lachlanchen/OpenHI/comparisons/align_background_vs_reference_code/DATASETS_DUAL.md

# Dual Three‑Panel Overlays (Blank + Sample + GT)

This note records the dual‑overlay figure that combines:
- **Blank** (light‑source only)
- **Sample** (dicot stem; previously mislabeled “sanqin”)
- **Ground‑truth spectrometer SPD**

The figure is generated by a dedicated script:
- `comparisons/align_background_vs_reference_code/compare_publication_three_panel_dual.py`

## Dataset Pairing (Lumileds)

**Blank segment**
- `scan_angle_20_lumileds/angle_20_blank_20250922_170433/angle_20_blank_event_20250922_170433_segments/Scan_1_Forward_events.npz`

**Sample segment (dicot stem)**
- `scan_angle_20_lumileds/angle_20_sanqin_20250922_170630/angle_20_sanqin_event_20250922_170630_segments/Scan_1_Forward_events.npz`

**Ground‑truth SPD**
- `comparisons/reference_spectrum_lumileds/USB2F042671_16-04-56-391.txt`

## Command Used (current best)

This run uses **auto‑shift by correlation** between the GT derivative and the
sample derivative. The auto‑shift consistently finds a shift near **‑49 nm**,
matching the manual observation but without hardcoding the value.

```bash
python comparisons/align_background_vs_reference_code/compare_publication_three_panel_dual.py \
  --segment-blank scan_angle_20_lumileds/angle_20_blank_20250922_170433/angle_20_blank_event_20250922_170433_segments/Scan_1_Forward_events.npz \
  --segment-sample scan_angle_20_lumileds/angle_20_sanqin_20250922_170630/angle_20_sanqin_event_20250922_170630_segments/Scan_1_Forward_events.npz \
  --gt_files comparisons/reference_spectrum_lumileds/USB2F042671_16-04-56-391.txt \
  --step_ms 2.0 --bin_ms 5.0 \
  --sensor_width 1280 --sensor_height 720 \
  --label-blank "Blank" --label-sample "Dicot stem" \
  --auto-shift-sample-corr --shift-range 120 --shift-step 1 \
  --suffix lumileds_blank_dicot_autoshift \
  --output_root comparisons/align_background_vs_reference_code
```

**Output**
- `comparisons/align_background_vs_reference_code/publication_20260206_213134/three_panel_dual_5ms_Scan_1_Forward_Scan_1_Forward_lumileds_blank_dicot_autoshift.png`
- `comparisons/align_background_vs_reference_code/publication_20260206_213134/three_panel_dual_5ms_Scan_1_Forward_Scan_1_Forward_lumileds_blank_dicot_autoshift_mapping.json`

## Alignment Logic (what changed and why)

Originally, the sample was aligned using **plateau‑based affine scaling**, which could push the curve below 0 and
produce unstable results. This is not robust when sample intensity has real absorption and does not share the
same plateau values as the blank/GT.

The alignment logic is now a **pure wavelength shift** for the sample:

- `--auto-shift-sample-corr` (recommended): shifts the sample to maximize correlation between
  the GT derivative and the sample derivative.
- `--sample-shift-nm` (manual): fixed shift in nm if you want full control.
- `--auto-shift-sample-left-edge` (optional): align left edge only.

This is **more stable** and keeps the sample curve shape intact while aligning the left edge
and overall derivative structure. No amplitude scaling is applied anymore.

## Notes

- The script uses **blank** to define the wavelength–time mapping (λ(t)).
- The sample shares the same mapping but can be shifted with `--sample-shift-nm`.
- If you want to try automatic left‑edge alignment, replace `--sample-shift-nm -50` with
  `--auto-shift-sample-left-edge`.
