lachlanchen/OpenHI/comparisons/align_background_vs_reference_code/publication_20260206_220756/background_trace_multibin_Scan_1_Forward_events.png

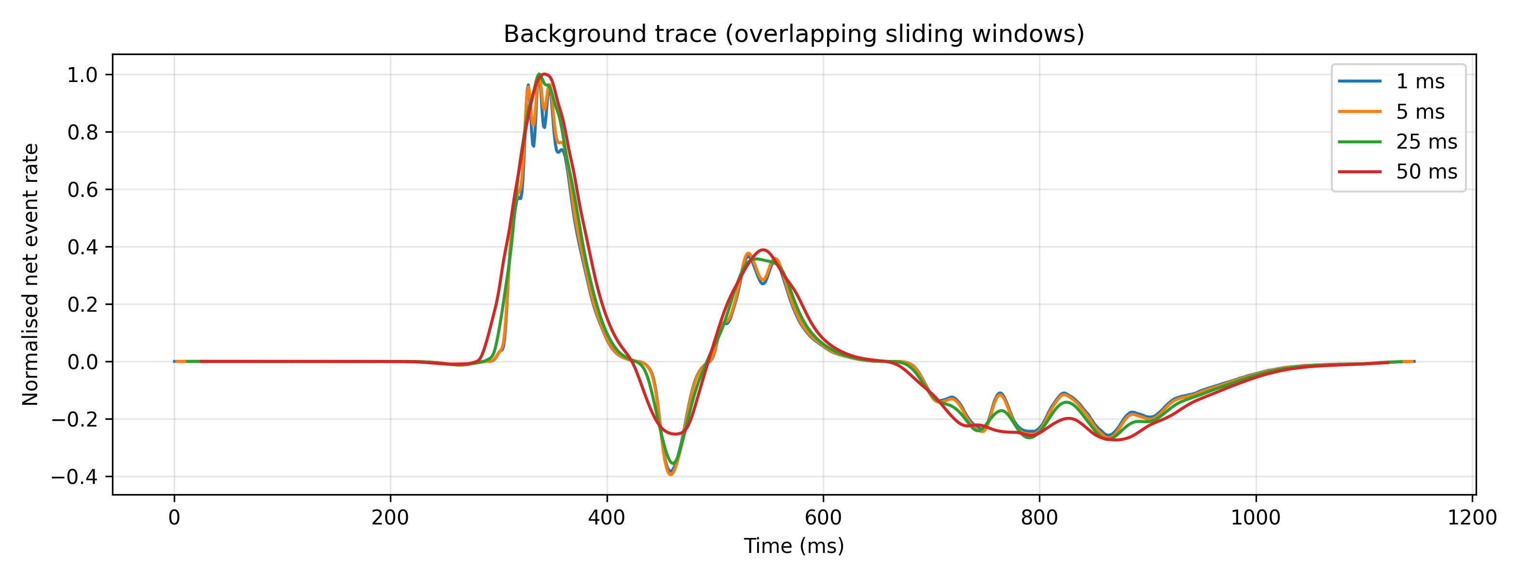
comparisons/align_background_vs_reference_code/publication_20260206_220756/background_trace_multibin_Scan_1_Forward_events.png
