lachlanchen/OpenHI/3D/Optional4F3D/Lens C holder.stl

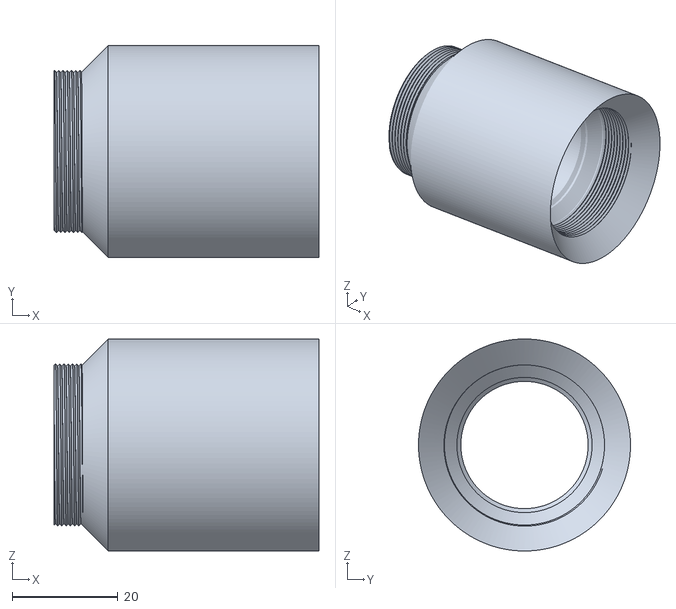
[picture p22: CAD file, 2026-03-04]
3D/Optional4F3D/Lens C holder.stl
50.0 x 40.0 x 40.0
