lachlanchen/OpenHI/3D/OpenHICoreModule3D/Motor cap.stl

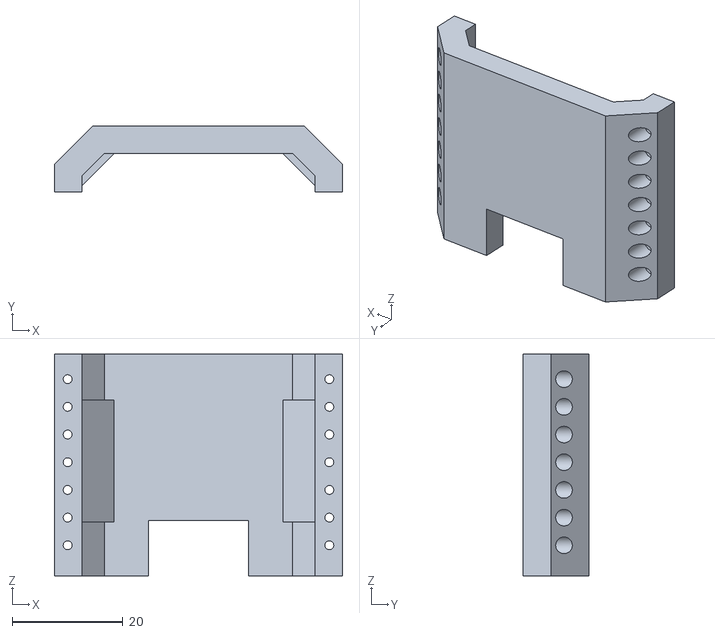
[picture p23: CAD file, 2026-03-04]
3D/OpenHICoreModule3D/Motor cap.stl
52.0 x 12.0 x 40.0
