lachlanchen/OpenHI/3D/OpenHICoreModule3D/Collimator holder FHPLP.stl

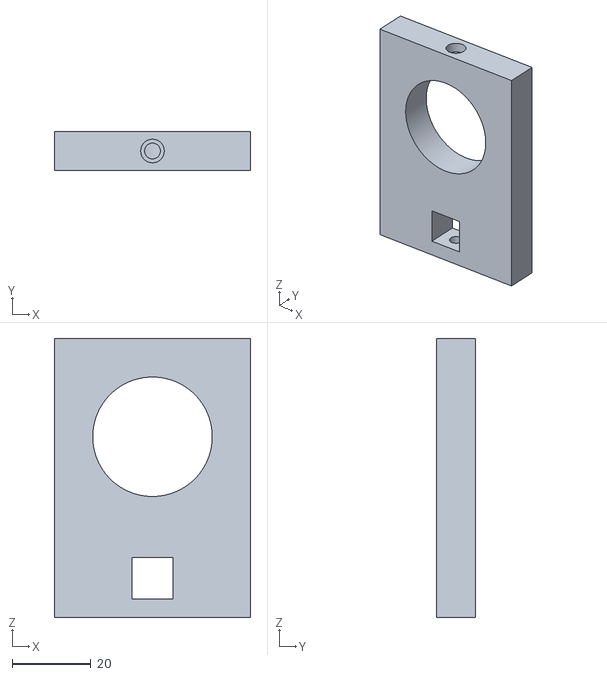
[picture p24: CAD file, 2026-03-04]
3D/OpenHICoreModule3D/Collimator holder FHPLP.stl
50.0 x 10.0 x 71.0
