lachlanchen/OpenHI/3D/OpenHICoreModule3D/Collimator cap.stl

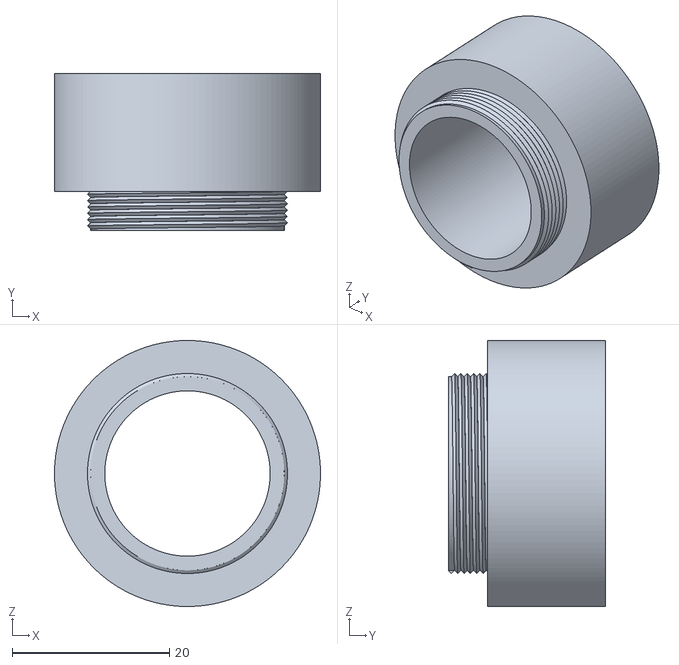
[picture p25: CAD file, 2026-03-04]
3D/OpenHICoreModule3D/Collimator cap.stl
33.8 x 20.0 x 33.8
