lachlanchen/OpenHI/3D/OpenHICoreModule3D/Motor holder.stl

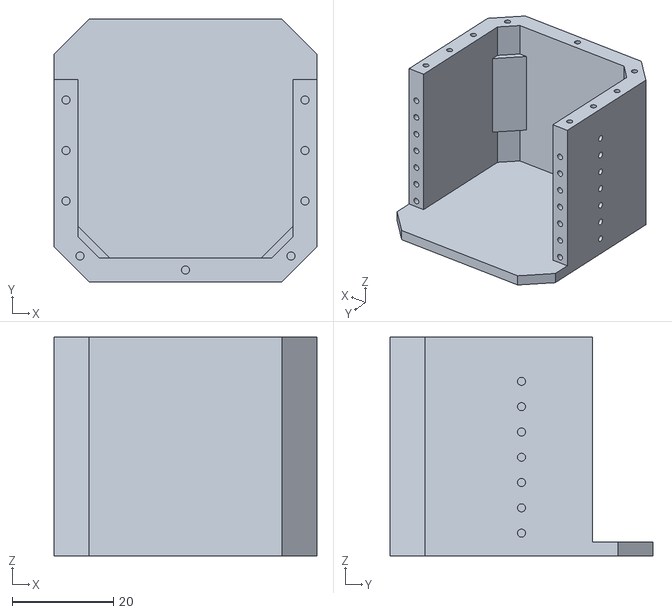
[picture p26: CAD file, 2026-03-04]
3D/OpenHICoreModule3D/Motor holder.stl
52.0 x 52.0 x 43.2
