lachlanchen/OpenHI/3D/OpenHICoreModule3D/LED holder.stl

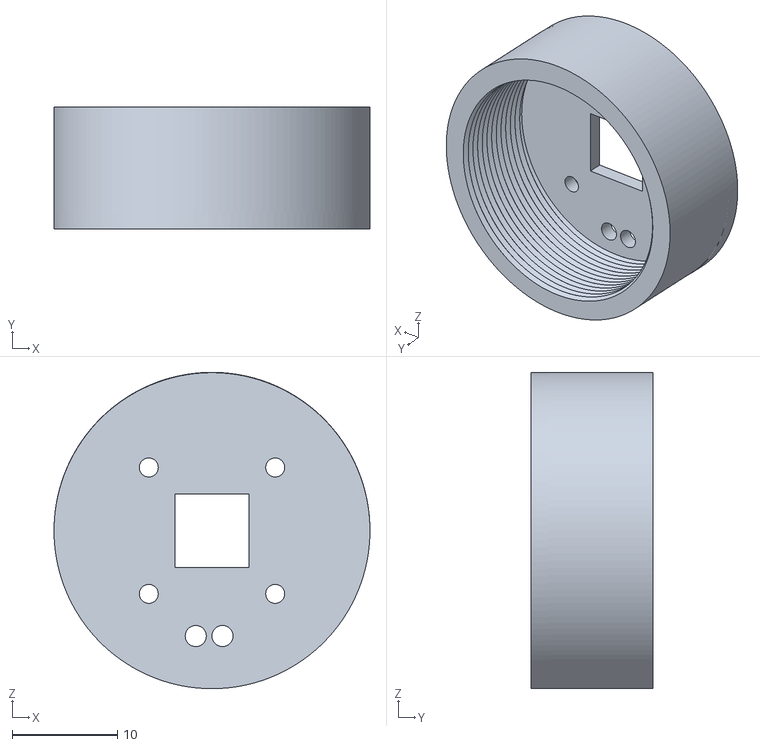
[picture p27: CAD file, 2026-03-04]
3D/OpenHICoreModule3D/LED holder.stl
30.0 x 11.6 x 30.0
