lachlanchen/OpenHI/3D/OpenHICoreModule3D/Sensor arm.stl

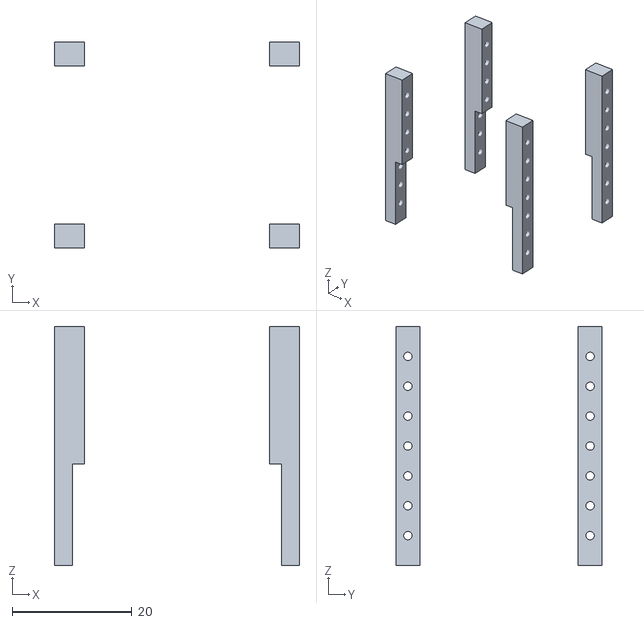
[picture p28: CAD file, 2026-03-04]
3D/OpenHICoreModule3D/Sensor arm.stl
41.0 x 34.5 x 40.0
